Al-Nafuur/United-Carts-of-Atari/source/Atari2600ROM/SmallCaps.asm

  MAC CHAR_D
    _CHAR_D {1}, 0, {2}
    _CHAR_D {1}, 1, {3}
    _CHAR_D {1}, 2, {4}
    _CHAR_D {1}, 3, {5}
    _CHAR_D {1}, 4, {6}
    _CHAR_D {1}, 5, {7}
    _CHAR_D {1}, 6, {8}
    _CHAR_D {1}, 7, {9}
    _CHAR_D {1}, 8, {10}
    _CHAR_D {1}, 9, {11}
    _CHAR_D {1}, 10, {12}
    _CHAR_D {1}, 11, {13}
  ENDM

  MAC CHAR_L
    _CHAR_L {1}, 0, {2}
    _CHAR_L {1}, 1, {3}
    _CHAR_L {1}, 2, {4}
    _CHAR_L {1}, 3, {5}
    _CHAR_L {1}, 4, {6}
    _CHAR_L {1}, 5, {7}
    _CHAR_L {1}, 6, {8}
    _CHAR_L {1}, 7, {9}
    _CHAR_L {1}, 8, {10}
    _CHAR_L {1}, 9, {11}
    _CHAR_L {1}, 10, {12}
    _CHAR_L {1}, 11, {13}
  ENDM

  MAC CHAR_R
    _CHAR_R {1}, 0, {2}
    _CHAR_R {1}, 1, {3}
    _CHAR_R {1}, 2, {4}
    _CHAR_R {1}, 3, {5}
    _CHAR_R {1}, 4, {6}
    _CHAR_R {1}, 5, {7}
    _CHAR_R {1}, 6, {8}
    _CHAR_R {1}, 7, {9}
    _CHAR_R {1}, 8, {10}
    _CHAR_R {1}, 9, {11}
    _CHAR_R {1}, 10, {12}
    _CHAR_R {1}, 11, {13}
  ENDM

    CHAR_D Blank, %0000, %0000, %0000, %0000, %0000, %0000, %0000, %0000, %0000, %0000, %0000, %0000
    CHAR_D Exclamation, %0010, %0010, %0010, %0010, %0010, %0010, %0010, %0010, %0000, %0000, %0010, %0010
    CHAR_D Quote, %0101, %0101, %0101, %0000, %0000, %0000, %0000, %0000, %0000, %0000, %0000, %0000
    CHAR_D Hash, %0000, %0001, %0101, %0111, %0111, %0101, %0101, %0111, %0111, %0101, %0100, %0000
    CHAR_D Dollar, %0010, %0011, %0111, %0110, %0110, %0111, %0011, %0011, %0011, %0111, %0110, %0010
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
  ENDIF

  IF NO_CONNECT = 2
    CHAR_L NoConnect, %0000, %0110, %0011, %0001, %0001, %1001, %1001, %0101, %0100, %0010, %0010, %0000
    CHAR_R NoConnect, %0000, %0010, %0010, %0001, %0101, %0100, %0100, %0100, %0100, %0110, %0011, %0000
  ENDIF

  IF NO_CONNECT = 3
    CHAR_L NoConnect, %0000, %0110, %0011, %1001, %1101, %1101, %1001, %1001, %1100, %0110, %0010, %0000
    CHAR_R NoConnect, %0000, %0010, %0011, %0001, %0100, %0100, %0101, %0101, %0100, %0110, %0011, %0000
  ENDIF

; Account
    CHAR_L Account, %1000, %1100, %1100, %1100, %1100, %1000, %0100, %0110, %1110, %1110, %1110, %1110
    CHAR_R Account, %0000, %0001, %0001, %0001, %0001, %0000, %0001, %0011, %0011, %0011, %0011, %0011

; NoAccount
    CHAR_L NoAccount, %1000, %0100, %0100, %0100, %0100, %1000, %0100, %0010, %0010, %0010, %0010, %0010
    CHAR_R NoAccount, %0000, %0001, %0001, %0001, %0001, %0000, %0001, %0010, %0010, %0010, %0010, %0010

; Page
    CHAR_L Page, %0111, %0111, %0100, %0101, %0101, %0101, %0101, %0111, %0111, %0001, %0001, %0001
    CHAR_R Page, %1100, %1100, %0100, %1111, %1111, %0001, %0001, %0001, %0001, %0001, %1111, %1111
