Al-Nafuur/United-Carts-of-Atari/source/STM32firmware/PlusCart/Inc/esp8266_AT_WiFiManager.h

/*
 * ESP8266 AT WiFi Manager templates based on:
 * https://github.com/tzapu/WiFiManager
 *
 */

#ifndef ESP8266_AT_WIFIMANAGER_H
#define	ESP8266_AT_WIFIMANAGER_H

#define GET_ROOT           " / "
#define GET_INDEX_HTML     " /index.html"
#define GET_FAVICON_ICO    " /favicon.ico"

#define GET_EXIT           "/exit"
#define GET_SAVE           "/save"
#define GET_NO_SCAN        "/0wifi"
#define GET_INFO           "/info"
#define GET_WIFI           "/wifi"
#define GET_PLUS_CONNECT   "/conn"
#define GET_SAVE_CONNECT   "/0save"

enum http_response_page{
	http_page_not_found,
	http_favicon_ico,
	http_page_start,
	http_page_exit,
	http_page_save,
	http_page_wifi_no_scan,
	http_page_info,
	http_page_wifi,
	http_page_plus_connect,
	http_page_plus_failed,
	http_page_plus_created,
	http_page_plus_connected,

};

typedef struct{
	char param[3];
	char *value;
}url_param;


const char html_head[]           = "<!DOCTYPE html><html lang=\"en\"><head><meta name=\"viewport\"content=\"width=device-width,initial-scale=1,user-scalable=no\"/><title>PlusCart(+) WiFi Manager Portal</title>"
                                   "<style> .c{text-align:center}div,input{padding:5px;font-size:1em}input{width:95%}a{color:#000}a:hover,a:active{color:red}body{text-align:center;font-family:verdana}button{border:0;border-radius:0.3rem;background-color:#67b9DD;color:#fff;line-height:2.4rem;font-size:1.2rem;width:100%;cursor:pointer} .q{float:right;width:64px;text-align:right} .l{background:url(\"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")no-repeat left center;background-size:1em} </style>"
                                   "<script>function c(l){document.getElementById('s').value=l.innerText||l.textContent;document.getElementById('p').focus();} </script>"
                                   "</head><body>"
		                           "<div style=\"background-image:linear-gradient(to right,#37609f 0%,#67b9DD 80%);color:#fff;margin:0 0 15px 0\"><h2>PlusCart(+)</h2><h3>WiFi Manager Portal</h3></div>"
                                   "<div style=\"text-align:left;display:inline-block;min-width:260px;\">";

const char html_portal_options[] = "<form action=\"" GET_WIFI "\"method=\"get\"><button>Configure WiFi</button></form><br/>"
		                           "<form action=\"" GET_NO_SCAN "\"method=\"get\"><button>Configure WiFi(No Scan)</button></form><br/>"
		                           "<form action=\"" GET_INFO "\"method=\"get\"><button>Connection Info</button></form><br/>"
		                           "<form action=\"" GET_EXIT "\"method=\"get\"><button>Exit</button></form>";

const char html_form[]           = "<form method='get'action='" GET_SAVE "'><input id='s'name='s'length=32 placeholder='SSID'><br/><input id='p'name='p'length=64 type='password'placeholder='password'><br/>"
                                   "<br/><button type='submit'>Save</button></form>"
								   "<br/><form action=\"" GET_WIFI "\"method=\"get\"><button>Rescan WiFi</button></form>";

const char html_plus_connect[]   = "<br/><form action=\"" GET_PLUS_CONNECT "\"method=\"get\"><button>PlusStore Connect</button></form>";

const char html_connect_form[]   = "<form method='get'action='" GET_SAVE_CONNECT "'><input id='s'name='s'length=32 placeholder='PlusStore User or Email'><br/>"
                                   "<br/><button type='submit'>Request Connect</button></form>";

const char html_back[]           = "</br><form action=\"/index.html\"method=\"get\"><button>Back</button></form>";


const char html_saved[]          = "<div>Credentials Saved<br/>Trying to connect WiFi module to network.<br/>"
		                           "To check if the action was successful go back to the main menu and click the Connection Info button.<br/>"
		                           "If it failed, restart the WiFi Manager Portal to try again</div>";

const char html_exit[]           = "<div>WiFi Manager closed. PlusCart is restarting.</div>";
const char html_plus_failed[]    = "<div>Connection request for your PlusCart failed, maybe the PlusCart is already connected?</div>";
const char html_plus_created[]   = "<div>PlusStore account for your email has been created, please check your mail and finish the registration.</div>";
const char html_plus_connected[] = "<div>Connection request for your PlusCart sent, please check your email and confirm.</div>";


const char html_end[]            = "</div></body></html>";


const char not_found_text[] = "HTTP/1.1 404 Not Found\n"
                              "Content-type: text/plain\r\n\r\n"
                              "page not found";

const char http_header_html[] = "HTTP/1.1 200 OK\n"
                                "Content-type: text/html\r\n\r\n";

const char favicon_ico[] = {
	// HTTP/1.1 200 OK
	// Content-type:image/x-icon
	0x48, 0x54, 0x54, 0x50, 0x2F, 0x31, 0x2E, 0x31, 0x20, 0x32, 0x30, 0x30, 0x20, 0x4F, 0x4B, 0x0A,
	0x43, 0x6F, 0x6E, 0x74, 0x65, 0x6E, 0x74, 0x2D, 0x74, 0x79, 0x70, 0x65, 0x3A, 0x20, 0x69, 0x6D,
	0x61, 0x67, 0x65, 0x2F, 0x78, 0x2D, 0x69, 0x63, 0x6F, 0x6E, 0x0D, 0x0A, 0x0D, 0x0A,
    // Content
	0x00, 0x00, 0x01, 0x00, 0x01, 0x00, 0x10, 0x10, 0x18, 0x00, 0x00, 0x00, 0x00, 0x00, 0x68, 0x03,
	0x00, 0x00, 0x16, 0x00, 0x00, 0x00, 0x28, 0x00, 0x00, 0x00, 0x10, 0x00, 0x00, 0x00, 0x20, 0x00,
	0x00, 0x00, 0x01, 0x00, 0x18, 0x00, 0x00, 0x00, 0x00, 0x00, 0x00, 0x03, 0x00, 0x00, 0x00, 0x00,
	0x00, 0x00, 0x00, 0x00, 0x00, 0x00, 0x00, 0x00, 0x00, 0x00, 0x00, 0x00, 0x00, 0x00, 0xE4, 0xBC,
	0x6A, 0xE2, 0xBA, 0x68, 0xD9, 0xB0, 0x61, 0xDC, 0xB3, 0x64, 0xCF, 0xA3, 0x56, 0xD2, 0xA6, 0x59,
	0xCC, 0x9D, 0x53, 0xC9, 0x9A, 0x50, 0xC5, 0x91, 0x4A, 0xC2, 0x8E, 0x47, 0xBD, 0x89, 0x43, 0xB8,
	0x84, 0x3E, 0xB0, 0x79, 0x36, 0xB1, 0x7A, 0x37, 0xAE, 0x74, 0x32, 0xA8, 0x6E, 0x2C, 0xE4, 0xBB,
	0x6C, 0xE0, 0xB9, 0x6B, 0xDC, 0xB6, 0x6E, 0xCF, 0xA9, 0x61, 0xD0, 0xA6, 0x5B, 0xCD, 0x9F, 0x52,
	0xD1, 0xA0, 0x54, 0xCB, 0x99, 0x4D, 0xCD, 0x98, 0x4F, 0xBC, 0x87, 0x3E, 0xC4, 0x8D, 0x48, 0xB9,
	0x85, 0x43, 0xB0, 0x7E, 0x42, 0xAB, 0x77, 0x3B, 0xAE, 0x78, 0x39, 0xA5, 0x6B, 0x2A, 0xEA, 0xC0,
	0x75, 0xD1, 0xAA, 0x65, 0x6F, 0x52, 0x19, 0x80, 0x62, 0x29, 0xD0, 0xA6, 0x63, 0xD4, 0xA3, 0x57,
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
	0xBE, 0x95, 0x57, 0x89, 0x62, 0x2B, 0x81, 0x5A, 0x23, 0xB0, 0x84, 0x49, 0xB8, 0x83, 0x40, 0xAF,
	0x7C, 0x3D, 0xA3, 0x7A, 0x4D, 0x32, 0x10, 0x00, 0x36, 0x14, 0x00, 0x81, 0x5F, 0x3B, 0xD1, 0xAC,
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
};

#endif	/* ESP8266_AT_WIFIMANAGER_H */
