Al-Nafuur/United-Carts-of-Atari/source/STM32firmware/PlusCart/Inc/fatfs.h

/**
  ******************************************************************************
  * @file   fatfs.h
  * @brief  Header for fatfs applications
  ******************************************************************************
  * @attention
  *
  * <h2><center>&copy; Copyright (c) 2021 STMicroelectronics.
  * All rights reserved.</center></h2>
  *
  * This software component is licensed by ST under Ultimate Liberty license
  * SLA0044, the "License"; You may not use this file except in compliance with
  * the License. You may obtain a copy of the License at:
  *                             www.st.com/SLA0044
  *
  ******************************************************************************
  */

/* Define to prevent recursive inclusion -------------------------------------*/
#ifndef __fatfs_H
#define __fatfs_H
#ifdef __cplusplus
 extern "C" {
#endif

#include "ff.h"
#include "ff_gen_drv.h"
#include "user_diskio.h" /* defines USER_Driver as external */

/* USER CODE BEGIN Includes */
#include "global.h"

/* USER CODE END Includes */

extern uint8_t retUSER; /* Return value for USER */
extern char USERPath[4]; /* USER logical drive path */
extern FATFS USERFatFS; /* File system object for USER logical drive */
extern FIL USERFile; /* File object for USER */

void MX_FATFS_Init(void);

/* USER CODE BEGIN Prototypes */
enum sd_card_stat{
	sd_card_total_size,
	sd_card_used_size,
};

bool sd_card_file_list( char *, MENU_ENTRY **dst, int * );
uint32_t sd_card_file_request( uint8_t *, const char *, uint32_t, uint32_t );
bool sd_card_find_file( char *, char *, MENU_ENTRY **dst, int * );
int sd_card_file_size( char * );
int * sd_card_statistic();
/* USER CODE END Prototypes */
#ifdef __cplusplus
}
#endif
#endif /*__fatfs_H */

/************************ (C) COPYRIGHT STMicroelectronics *****END OF FILE****/
