Al-Nafuur/United-Carts-of-Atari/source/STM32firmware/PlusCart/Inc/cartridge_emulation_ar.h

#ifndef CARTRIDGE_EMULATION_AR_H
#define CARTRIDGE_EMULATION_AR_H

void emulate_ar_cartridge(const char* filename, unsigned int image_size, uint8_t *buffer, int tv_mode, MENU_ENTRY *d );

#endif // CARTRIDGE_EMULATION_AR_H
